marcass/grinder_timer/kicad/kicad_lib/KiCad-Libraries-master/3D/SourceFiles/MPU9150/MPU9150-SCAD.stl

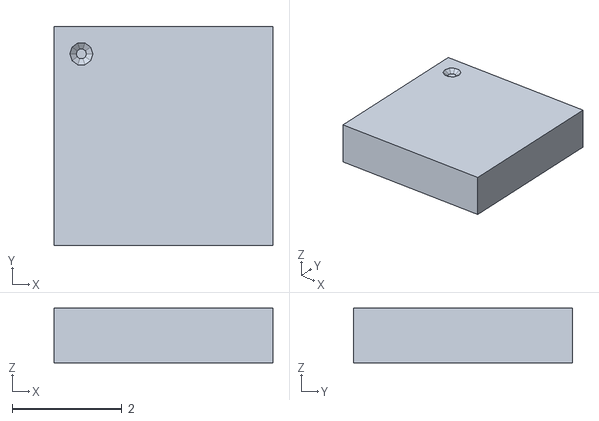
[picture p17: CAD file, 2017-02-18]
kicad/kicad_lib/KiCad-Libraries-master/3D/SourceFiles/MPU9150/MPU9150-SCAD.stl
4.00 x 4.00 x 1.00
