marcass/grinder_timer/kicad/kicad_lib/KiCad-Libraries-master/3D/SourceFiles/Sensors/SHARP_GP1A57HRJ00F-wings.stl

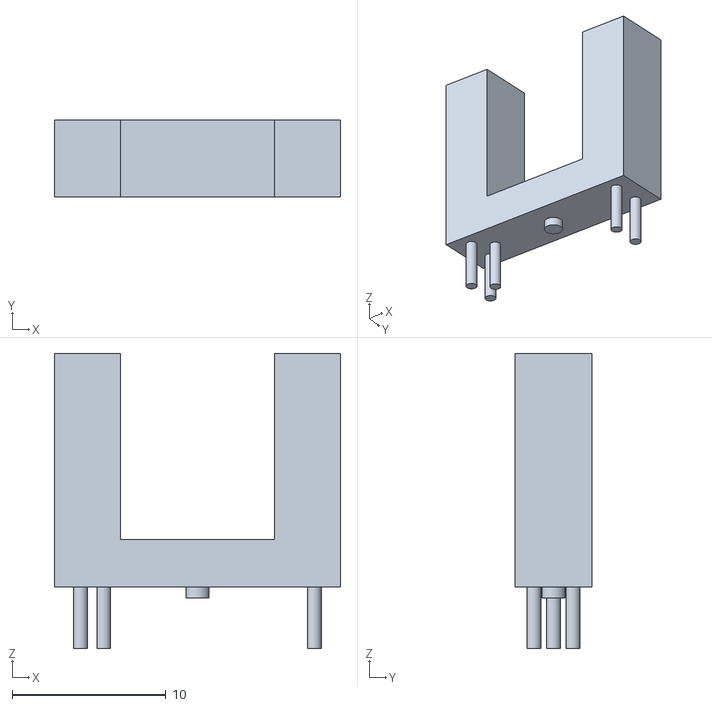
[picture p19: CAD file, 2017-02-18]
kicad/kicad_lib/KiCad-Libraries-master/3D/SourceFiles/Sensors/SHARP_GP1A57HRJ00F-wings.stl
18.6 x 5.00 x 19.2
