marcass/grinder_timer/kicad/kicad_lib/KiCad-Libraries-master/3D/SourceFiles/SMD_Passives/SMD-1206-scad.stl

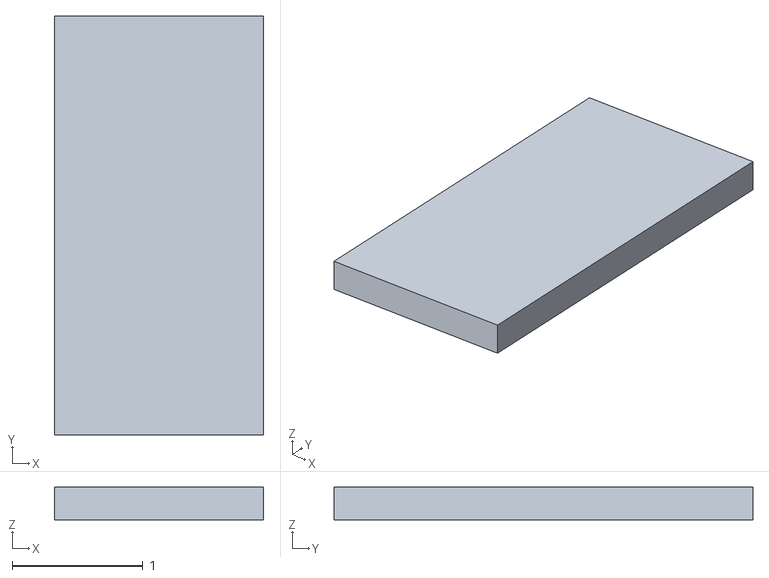
[picture p20: CAD file, 2017-02-18]
kicad/kicad_lib/KiCad-Libraries-master/3D/SourceFiles/SMD_Passives/SMD-1206-scad.stl
1.60 x 3.20 x 0.25
