marcass/grinder_timer/kicad/kicad_lib/KiCad-Libraries-master/3D/SourceFiles/SOIC/SOIC_08_4.0mm_5.0mm_1.27mm-wings.stl

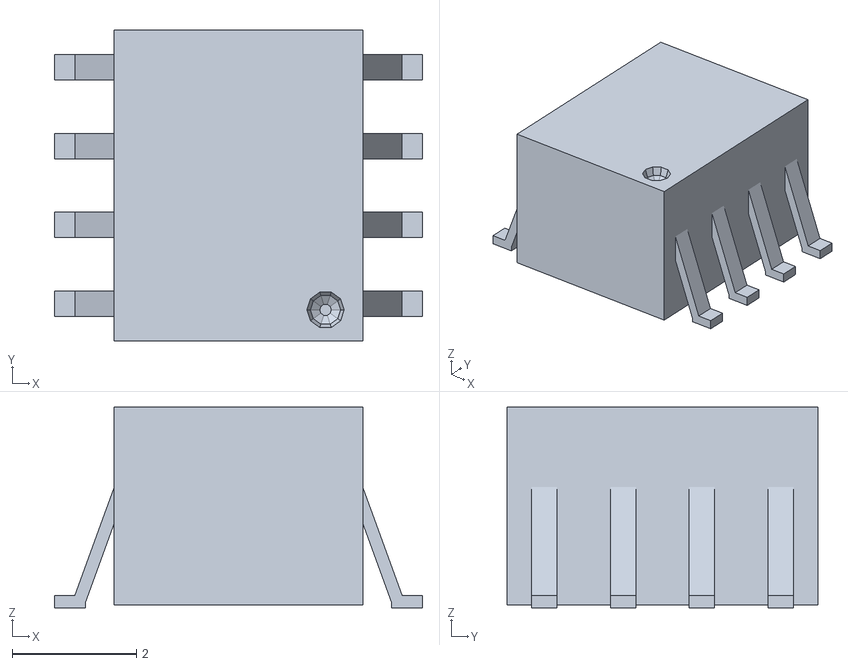
[picture p21: CAD file, 2017-02-18]
kicad/kicad_lib/KiCad-Libraries-master/3D/SourceFiles/SOIC/SOIC_08_4.0mm_5.0mm_1.27mm-wings.stl
5.92 x 5.00 x 3.23
