marcass/grinder_timer/kicad/kicad_lib/KiCad-Libraries-master/3D/SourceFiles/SolarCells/Spectrolab_CIC-Wings.stl.stl

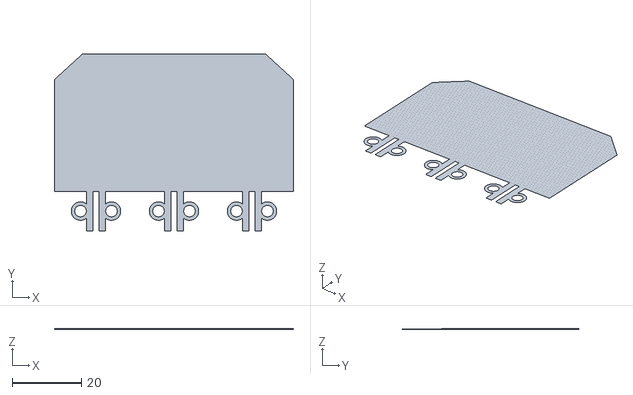
[picture p22: CAD file, 2017-02-18]
kicad/kicad_lib/KiCad-Libraries-master/3D/SourceFiles/SolarCells/Spectrolab_CIC-Wings.stl.stl
69.1 x 51.1 x 0.178
