marcass/grinder_timer/kicad/kicad_lib/KiCad-Libraries-master/3D/SourceFiles/SON-10/SON-10-wings.stl

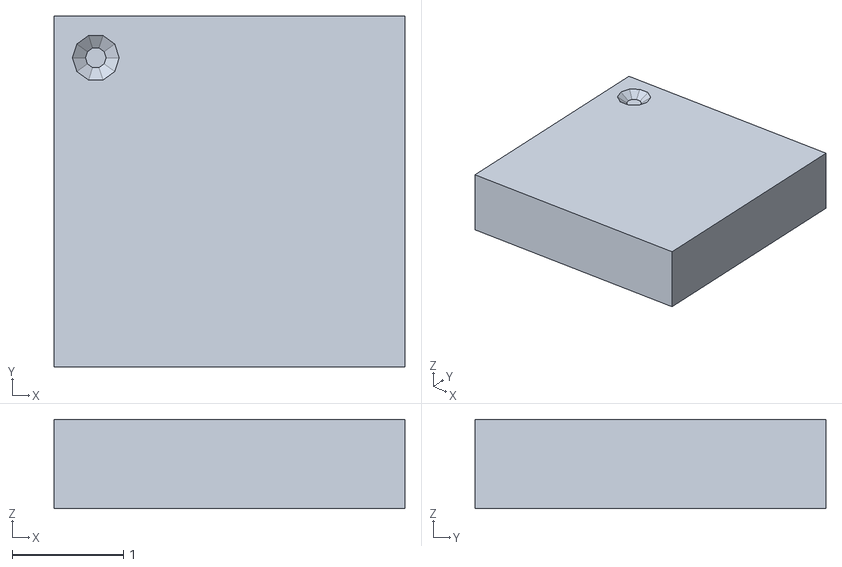
[picture p23: CAD file, 2017-02-18]
kicad/kicad_lib/KiCad-Libraries-master/3D/SourceFiles/SON-10/SON-10-wings.stl
3.15 x 3.15 x 0.8
