marcass/grinder_timer/kicad/kicad_lib/KiCad-Libraries-master/3D/SourceFiles/SOT-23/SOT-23-6-wings.stl

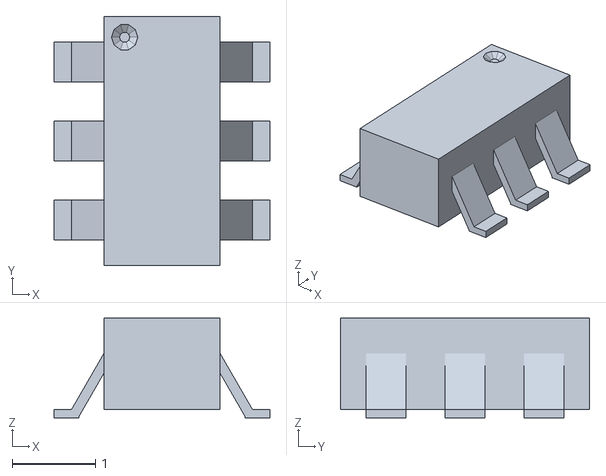
[picture p24: CAD file, 2017-02-18]
kicad/kicad_lib/KiCad-Libraries-master/3D/SourceFiles/SOT-23/SOT-23-6-wings.stl
2.60 x 3.00 x 1.20
