marcass/grinder_timer/kicad/kicad_lib/KiCad-Libraries-master/3D/SourceFiles/SOT-363/SOT-363-Wings.stl

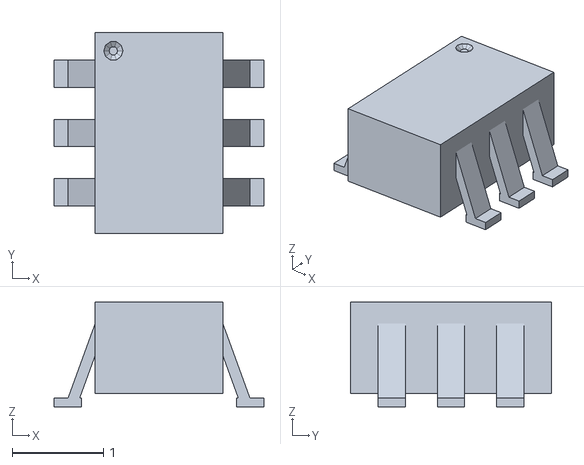
[picture p25: CAD file, 2017-02-18]
kicad/kicad_lib/KiCad-Libraries-master/3D/SourceFiles/SOT-363/SOT-363-Wings.stl
2.30 x 2.20 x 1.15
