marcass/grinder_timer/kicad/kicad_lib/KiCad-Libraries-master/3D/SourceFiles/SSOP/SSOP_08_3.0mm_2.0mm_0.5mm-wings.stl

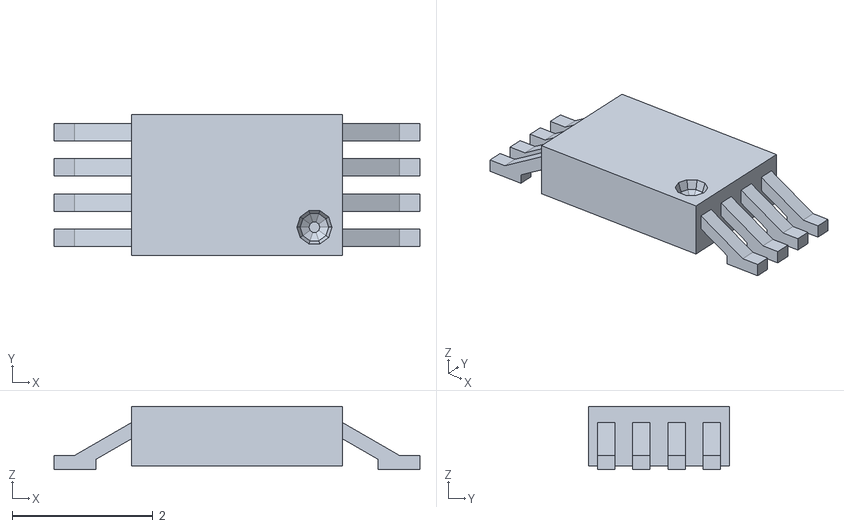
[picture p26: CAD file, 2017-02-18]
kicad/kicad_lib/KiCad-Libraries-master/3D/SourceFiles/SSOP/SSOP_08_3.0mm_2.0mm_0.5mm-wings.stl
5.20 x 2.00 x 0.9
