marcass/grinder_timer/kicad/kicad_lib/KiCad-Libraries-master/3D/SourceFiles/Switches/Switch-TE-Slide-Wings.stl

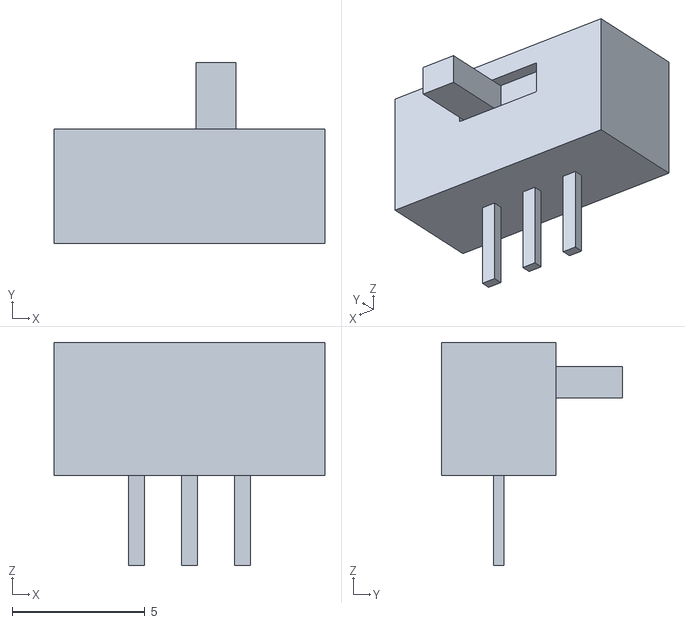
[picture p27: CAD file, 2017-02-18]
kicad/kicad_lib/KiCad-Libraries-master/3D/SourceFiles/Switches/Switch-TE-Slide-Wings.stl
10.2 x 6.80 x 8.40
