marcass/grinder_timer/kicad/kicad_lib/KiCad-Libraries-master/3D/SourceFiles/Venus638/Venus638-Wings.stl

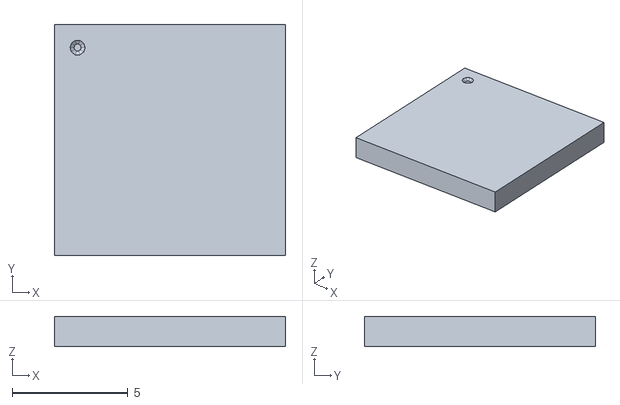
[picture p28: CAD file, 2017-02-18]
kicad/kicad_lib/KiCad-Libraries-master/3D/SourceFiles/Venus638/Venus638-Wings.stl
10.0 x 10.0 x 1.30
