marcass/grinder_timer/kicad/kicad_lib/KiCad-Libraries-master/3D/SourceFiles/Connectors/CONN_1x6/CONN_1x6_Female.stl

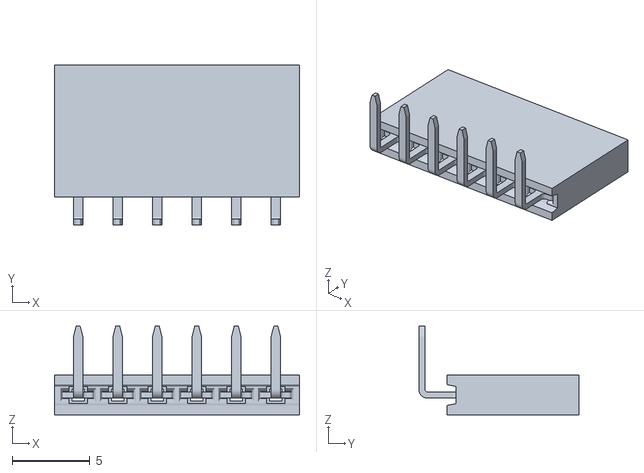
[picture p29: CAD file, 2017-02-18]
kicad/kicad_lib/KiCad-Libraries-master/3D/SourceFiles/Connectors/CONN_1x6/CONN_1x6_Female.stl
15.7 x 10.3 x 5.69
