marcass/grinder_timer/kicad/kicad_lib/KiCad-Libraries-master/3D/SourceFiles/Connectors/CONN_2x6/CONN_2x6_Male.stl

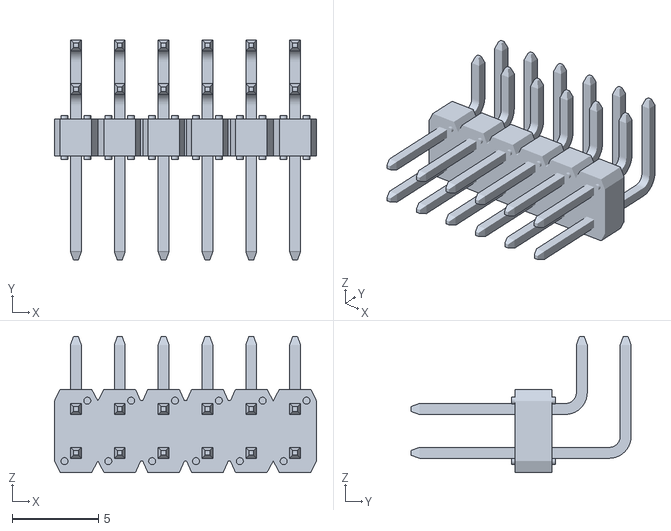
[picture p30: CAD file, 2017-02-18]
kicad/kicad_lib/KiCad-Libraries-master/3D/SourceFiles/Connectors/CONN_2x6/CONN_2x6_Male.stl
15.2 x 12.8 x 7.89
