marcass/grinder_timer/kicad/kicad_lib/KiCad-Libraries-master/3D/SourceFiles/SD_Objects/SD-Amp-microSlot-SCAD.stl

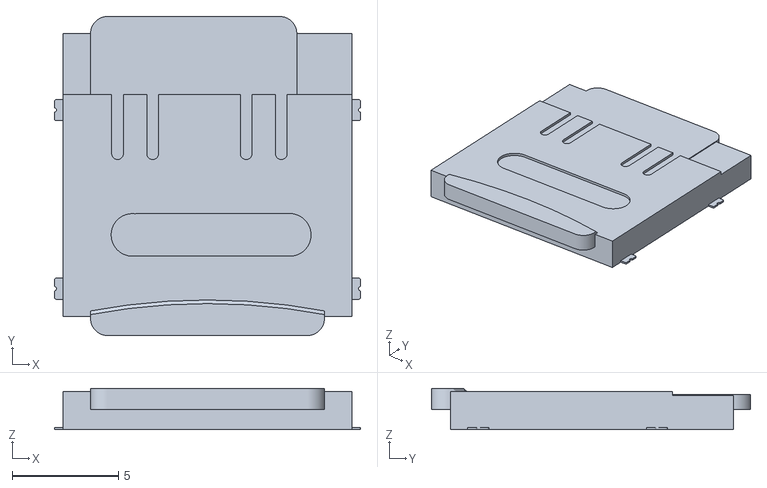
[picture p31: CAD file, 2017-02-18]
kicad/kicad_lib/KiCad-Libraries-master/3D/SourceFiles/SD_Objects/SD-Amp-microSlot-SCAD.stl
14.4 x 15.0 x 1.95
