marcass/grinder_timer/kicad/kicad_lib/KiCad-Libraries-master/3D/SourceFiles/SMD_Passives/SMD-0805-scad.stl

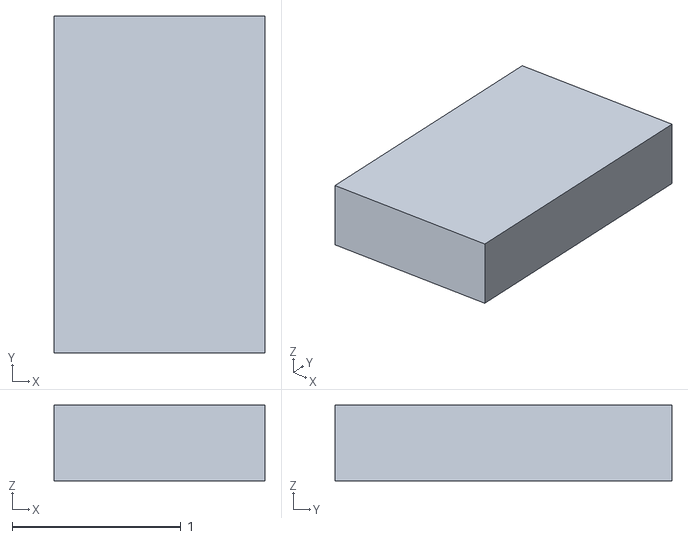
[picture p32: CAD file, 2017-02-18]
kicad/kicad_lib/KiCad-Libraries-master/3D/SourceFiles/SMD_Passives/SMD-0805-scad.stl
1.25 x 2.00 x 0.45
