marcass/grinder_timer/kicad/kicad_lib/KiCad-Libraries-master/3D/SourceFiles/SolarCells/Spectrolab_TASC1-SCAD.stl

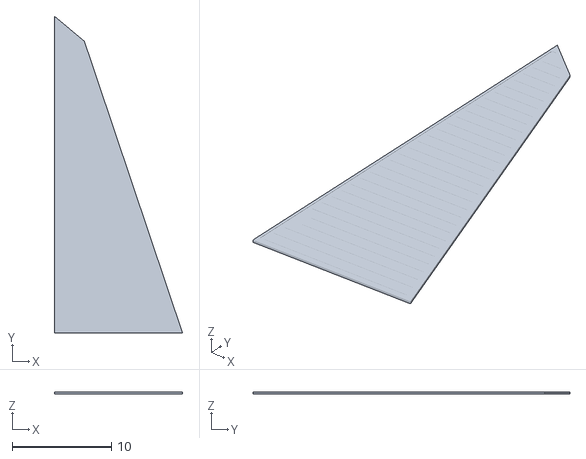
[picture p33: CAD file, 2017-02-18]
kicad/kicad_lib/KiCad-Libraries-master/3D/SourceFiles/SolarCells/Spectrolab_TASC1-SCAD.stl
12.9 x 31.9 x 0.178
