marcass/grinder_timer/kicad/kicad_lib/KiCad-Libraries-master/3D/SourceFiles/SON-10/SON-10-scad.stl

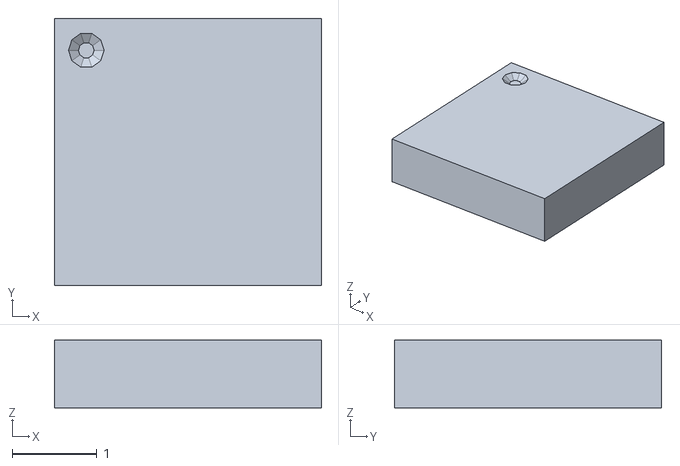
[picture p34: CAD file, 2017-02-18]
kicad/kicad_lib/KiCad-Libraries-master/3D/SourceFiles/SON-10/SON-10-scad.stl
3.15 x 3.15 x 0.8
