marcass/grinder_timer/kicad/kicad_lib/KiCad-Libraries-master/3D/SourceFiles/Switches/Switch-DIP-SMD-3-SCAD.stl

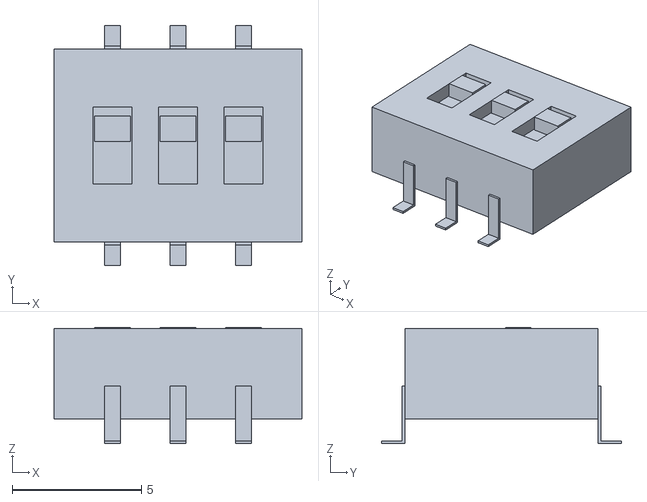
[picture p35: CAD file, 2017-02-18]
kicad/kicad_lib/KiCad-Libraries-master/3D/SourceFiles/Switches/Switch-DIP-SMD-3-SCAD.stl
9.60 x 9.30 x 4.50
