marcass/grinder_timer/kicad/kicad_lib/KiCad-Libraries-master/3D/SourceFiles/Connectors/Deans/DeansMicro-SCAD.stl

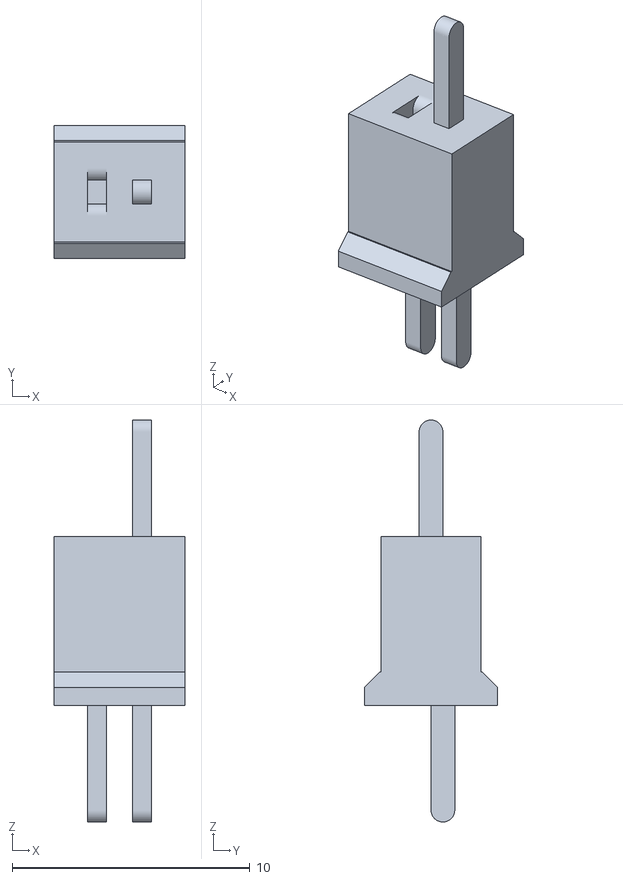
[picture p36: CAD file, 2017-02-18]
kicad/kicad_lib/KiCad-Libraries-master/3D/SourceFiles/Connectors/Deans/DeansMicro-SCAD.stl
5.50 x 5.60 x 16.9
