marcass/grinder_timer/kicad/kicad_lib/KiCad-Libraries-master/3D/SourceFiles/SMD_Passives/SMD-2010-wings.stl

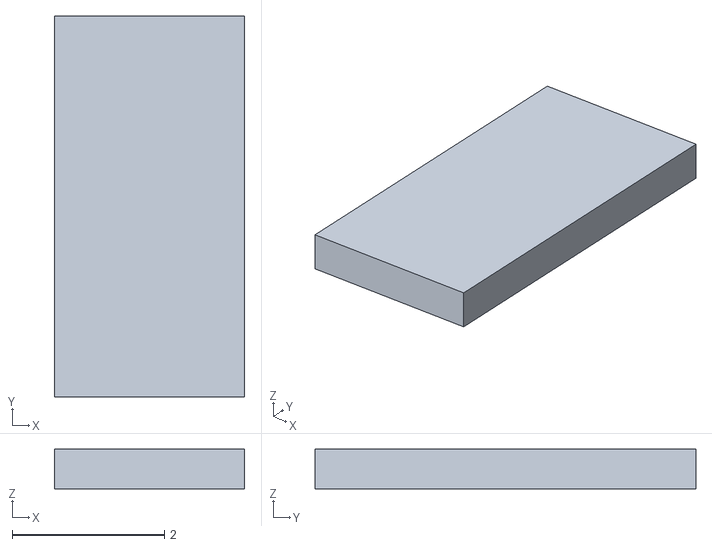
[picture p37: CAD file, 2017-02-18]
kicad/kicad_lib/KiCad-Libraries-master/3D/SourceFiles/SMD_Passives/SMD-2010-wings.stl
2.50 x 5.00 x 0.52
