marcass/grinder_timer/kicad/kicad_lib/KiCad-Libraries-master/3D/SourceFiles/SOIC/SOIC_08_4.0mm_5.8mm_1.27mm-scad.stl

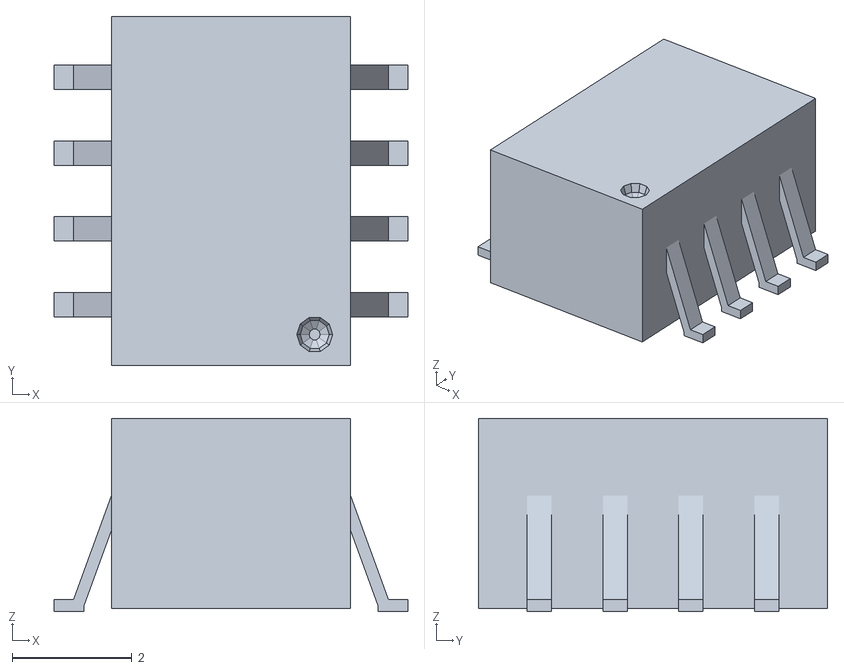
[picture p38: CAD file, 2017-02-18]
kicad/kicad_lib/KiCad-Libraries-master/3D/SourceFiles/SOIC/SOIC_08_4.0mm_5.8mm_1.27mm-scad.stl
5.92 x 5.84 x 3.23
