marcass/grinder_timer/kicad/kicad_lib/KiCad-Libraries-master/3D/SourceFiles/SSOP/SSOP_20_4.5mm_6.6mm_0.65mm-scad.stl

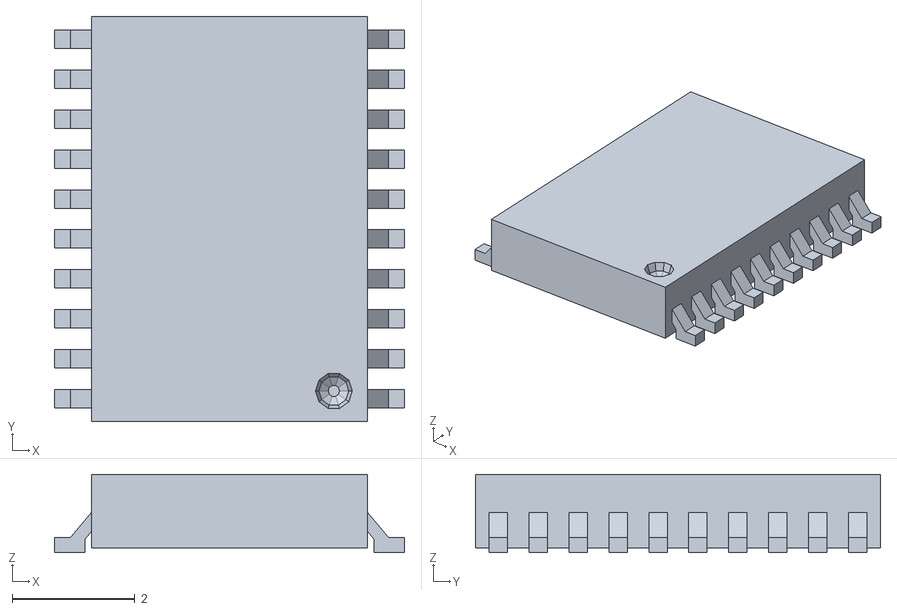
[picture p39: CAD file, 2017-02-18]
kicad/kicad_lib/KiCad-Libraries-master/3D/SourceFiles/SSOP/SSOP_20_4.5mm_6.6mm_0.65mm-scad.stl
5.70 x 6.60 x 1.27
