marcass/grinder_timer/kicad/kicad_lib/KiCad-Libraries-master/3D/SourceFiles/SSOP/SSOP_08_3.0mm_3.0mm_0.65mm-scad.stl

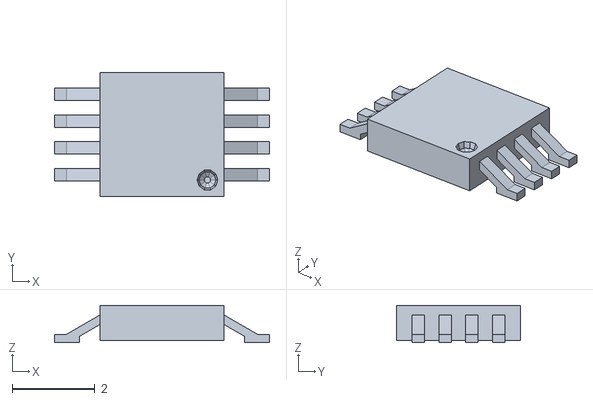
[picture p40: CAD file, 2017-02-18]
kicad/kicad_lib/KiCad-Libraries-master/3D/SourceFiles/SSOP/SSOP_08_3.0mm_3.0mm_0.65mm-scad.stl
5.20 x 3.00 x 0.9
