marcass/grinder_timer/kicad/kicad_lib/KiCad-Libraries-master/3D/SourceFiles/Switches/Switch-Eswitch-Slide-SCAD.stl

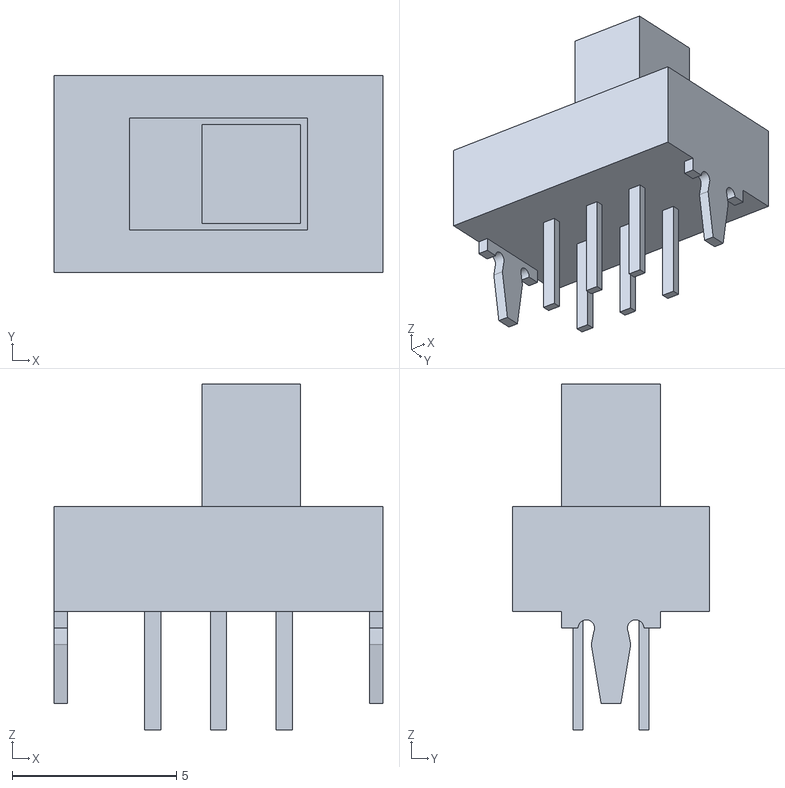
[picture p41: CAD file, 2017-02-18]
kicad/kicad_lib/KiCad-Libraries-master/3D/SourceFiles/Switches/Switch-Eswitch-Slide-SCAD.stl
10.0 x 6.00 x 10.5
